Fescron/masterthesis/firmware/EFM32HG222F64_iot-mbbr/inc/credentials.h

/***************************************************************************//**
 * @file credentials.h
 * @brief Header file containing DEVICE_ID and DEVICE_ID.
 * @version 1.0
 * @author Brecht Van Eeckhoudt
 *
 ******************************************************************************/


/* Include guards prevent multiple inclusions of the same header */
#ifndef _CREDENTIALS_H_
#define _CREDENTIALS_H_


/* deviceID \n deviceToken \n deviceState */
#define DEVICE_ID        "************************"
#define DEVICE_TOKEN     "maker:****************************************"


#endif /* _CREDENTIALS_H_ */
